HalmonCelman/RetCon/program/Core/KS0108_lib/graphic.c

#include "graphic.h"

extern void GLCD_SetPixel(unsigned char x, unsigned char y, unsigned char color);

const unsigned char color = 1;

void GLCD_Rectangle(unsigned char x, unsigned char y, unsigned char b, unsigned char a)
{
  unsigned char j; // zmienna pomocnicza
  // rysowanie linii pionowych (boki)
  for (j = 0; j < a; j++) {
		GLCD_SetPixel(x, y + j, color);
		GLCD_SetPixel(x + b - 1, y + j, color);
	}
  // rysowanie linii poziomych (podstawy)
  for (j = 0; j < b; j++)	{
		GLCD_SetPixel(x + j, y, color);
		GLCD_SetPixel(x + j, y + a - 1, color);
	}
}
//

void GLCD_Circle(unsigned char cx, unsigned char cy ,unsigned char radius)
{
int x, y, xchange, ychange, radiusError;
x = radius;
y = 0;
xchange = 1 - 2 * radius;
ychange = 1;
radiusError = 0;
while(x >= y)
  {
  GLCD_SetPixel(cx+x, cy+y, color); 
  GLCD_SetPixel(cx-x, cy+y, color); 
  GLCD_SetPixel(cx-x, cy-y, color);
  GLCD_SetPixel(cx+x, cy-y, color); 
  GLCD_SetPixel(cx+y, cy+x, color); 
  GLCD_SetPixel(cx-y, cy+x, color); 
  GLCD_SetPixel(cx-y, cy-x, color); 
  GLCD_SetPixel(cx+y, cy-x, color); 
  y++;
  radiusError += ychange;
  ychange += 2;
  if ( 2*radiusError + xchange > 0 )
    {
    x--;
	radiusError += xchange;
	xchange += 2;
	}
  }
}
//

void GLCD_Line(unsigned int X1,unsigned int Y1,unsigned int X2,unsigned int Y2)
{
int CurrentX, CurrentY, Xinc, Yinc, 
    Dx, Dy, TwoDx, TwoDy, 
	TwoDxAccumulatedError, TwoDyAccumulatedError;

Dx = (X2-X1);
Dy = (Y2-Y1);

TwoDx = Dx + Dx;
TwoDy = Dy + Dy;

CurrentX = X1; // zaczynamy od X1
CurrentY = Y1; // oraz Y1

Xinc = 1;
Yinc = 1;

if(Dx < 0)
  {
  Xinc = -1;
  Dx = -Dx;
  TwoDx = -TwoDx;
  }

if (Dy < 0)
  {
  Yinc = -1;
  Dy = -Dy;
  TwoDy = -TwoDy;
  }

GLCD_SetPixel(X1,Y1, color); // stawiamy pierwszy krok (zapalamy pierwszy piksel)

if ((Dx != 0) || (Dy != 0))
  {

  if (Dy <= Dx)
    { 
    TwoDxAccumulatedError = 0;
    do
	  {
      CurrentX += Xinc; // do aktualnej pozycji dodajemy krok 
      TwoDxAccumulatedError += TwoDy;
      if(TwoDxAccumulatedError > Dx)
        {
        CurrentY += Yinc;
        TwoDxAccumulatedError -= TwoDx; // i odejmujemy TwoDx
        }
       GLCD_SetPixel(CurrentX,CurrentY, color);
       }while (CurrentX != X2);
     }
   else // w przeciwnym razie idziemy "po igrekach" 
      {
      TwoDyAccumulatedError = 0; 
      do 
	    {
        CurrentY += Yinc; 
        TwoDyAccumulatedError += TwoDx;
        if(TwoDyAccumulatedError>Dy) 
          {
          CurrentX += Xinc;
          TwoDyAccumulatedError -= TwoDy;
          }
         GLCD_SetPixel(CurrentX,CurrentY, color); 
         }while (CurrentY != Y2);
    }
  }
}
//
